eavm512/ME396P-F2022-G03/Standards/brainstorm data structure/board-class-rack.jpeg

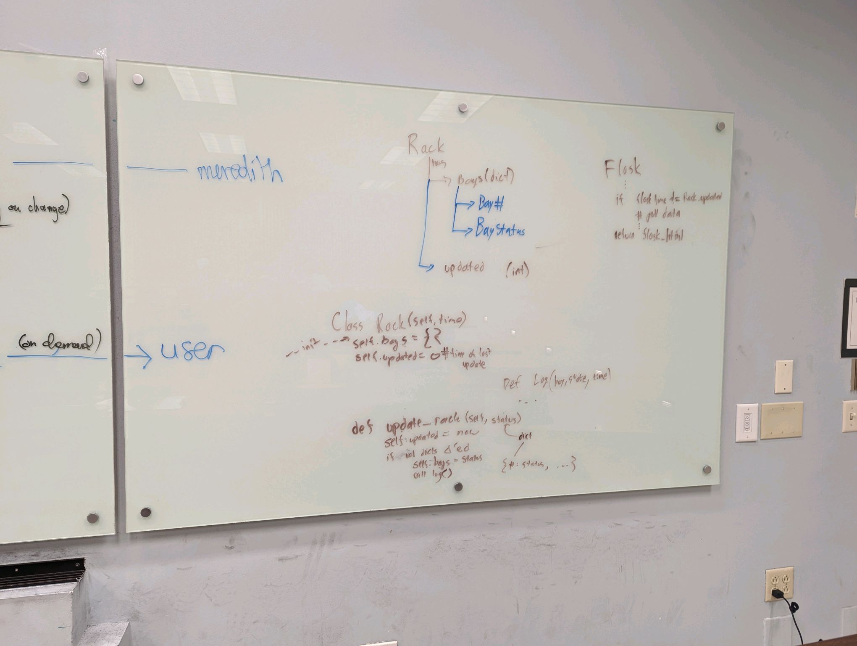
Standards/brainstorm data structure/board-class-rack.jpeg
