eavm512/ME396P-F2022-G03/Lightning Talk and Demo-test files/basic_arduino_game/basic_arduino_game.png

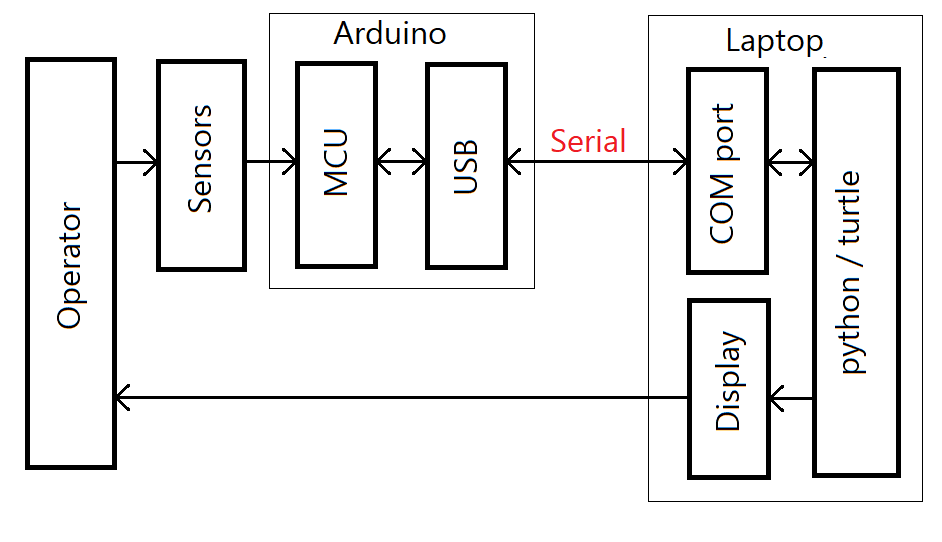
Lightning Talk and Demo-test files/basic_arduino_game/basic_arduino_game.png
