eavm512/ME396P-F2022-G03/Lightning Talk and Demo-test files/button-LED.png

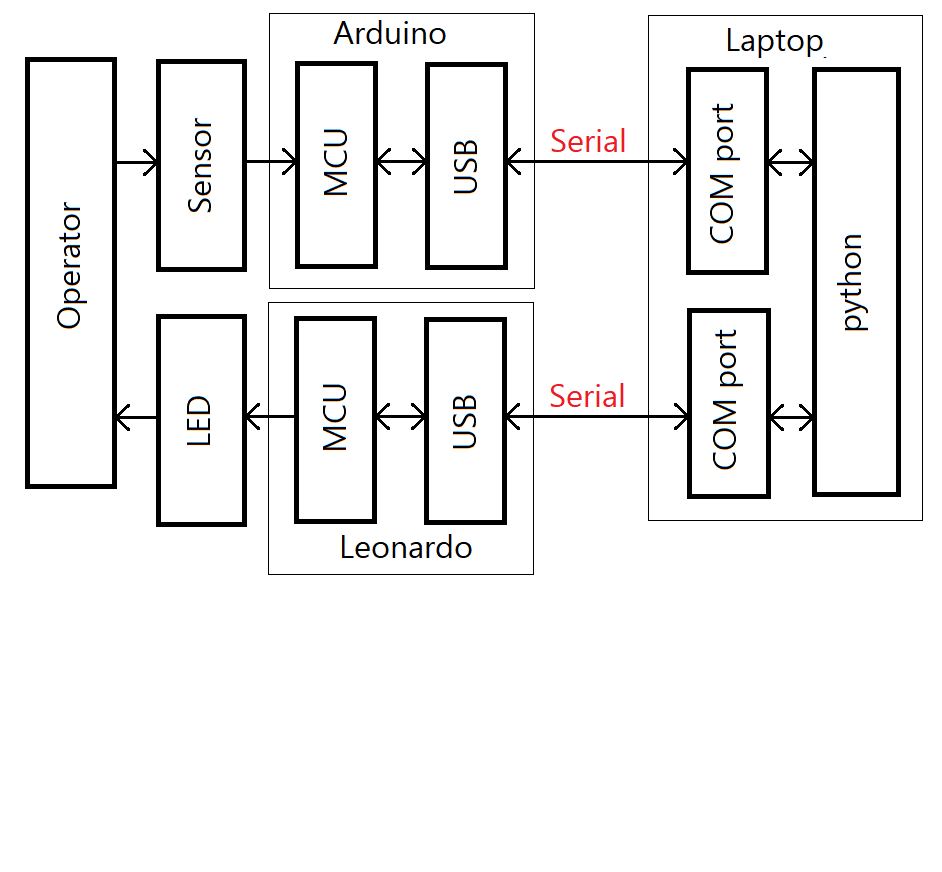
Lightning Talk and Demo-test files/button-LED.png
