eavm512/ME396P-F2022-G03/Lightning Talk and Demo-test files/basic_arduino_game/basic_game_controller.py

# -*- coding: utf-8 -*-
"""
Python 3.7
Created on Sat Oct  8 10:24:00 2022

@author: casso
"""

import serial
import turtle
import time

# ser = serial.Serial('COM3', 9600)

# ser
# Out[5]: Serial<id=0x254b51f4c70, open=True>(port='COM3', baudrate=9600, bytesize=8, parity='N', stopbits=1, timeout=None, xonxoff=False, rtscts=False, dsrdtr=False)

# ser.readline()
# Out[6]: b'17697\r\n'

#go get some test input lines
# ser = serial.Serial('COM3', 9600)
# lines = []
# while len(lines) < 10:
#     lines.append(ser.readline())
    
# #parse the lines
# messages = []
# for line in lines:
#     message = ''
#     decoded = bytes.decode(line)
    
#     for char in decoded:
#         if char != '\n' and char != '\r':
#             message = message + char
    
#     messages.append(message)
    
# #see how we did
# print(messages)
#   ['108', 'FIRE!', '153', '133', '147', '233', 'FIRE!', '273', '290', 'FIRE!']
# ser.close()

def test_serial(ser):
    lines = []
    while len(lines) < 10:
        lines.append(ser.readline())
        
    #parse the lines
    messages = []
    for line in lines:
        message = ''
        decoded = bytes.decode(line)
        
        for char in decoded:
            if char != '\n' and char != '\r':
                message = message + char
        
        messages.append(message)
    
    return messages

def parse_msg(msg_str):
    msg_str = bytes.decode(msg_str)
    msg = ''
    for char in msg_str:
        if char != '\n' and char != '\r':
            msg += char
    return msg

def shoot(current_angle):
    '''shoot a projectile
    '''
    missile = turtle.Turtle()
    missile.lt(current_angle)
    missile.penup()
    
    #make it a laser if we're in laser mode
    if projectile_mode == 'laser':
        missile.speed(speed = 0) #spin laser turtle FAST
        missile.pendown()
        missile.pen(fillcolor = 'red', pencolor = 'red')
        missile.ht() #hide the turtle     
    
    return missile

def draw(msg, missiles, last_heading, projectile_mode):
    '''
    rotate the player
    advance any missiles
    remove any missiles that have gone too far
    '''
    print(msg)    

    
    if msg != 'FIRE!' and msg != 'Toggle mode':
        last_heading = int(msg)
        player.settiltangle(last_heading)
    elif 'Toggle mode' in msg:
        if projectile_mode == 'arrow': 
            projectile_mode = 'laser'
        else: 
            projectile_mode = 'arrow'
    else: #we're firing a missile!
        new_missile = shoot(last_heading)
        missiles.append(new_missile)
        print('pew!')
    
    #advance existing missiles
    for miss in missiles:
        if miss.pencolor() == 'red':
            miss.forward(LASER_SPEED)
        else:
            miss.forward(MISSILE_SPEED)

    
    #remove missiles that are far away:
    #someone help me with a better way to do this!
    to_remove = []
    for idx in range(0, len(missiles)):
        if missiles[idx].distance(0,0) > MISSILE_DELETE:
            to_remove.append(idx)
            
    to_remove.reverse()
    for remove_idx in to_remove:
        missiles[remove_idx].reset()
        missiles[remove_idx].ht() #hide the turtle
        del missiles[remove_idx]
    
    
    return missiles, last_heading, projectile_mode

#--------------------------------------------------
MISSILE_DELETE = 220
MISSILE_SPEED  = 10
MISSILE_COLOR  = 'off'
LASER_SPEED = 200
LASER_TRAIL = 'red'
TURTLE_SPEED = 1 #Faster than turtle's default. pick 0-10, 0 fastest

projectile_mode = 'arrow'
projectile_speed = MISSILE_SPEED
projectile_color = 'off'

ser =serial.Serial('COM3', 9600)

player = turtle.Turtle()
player.shape('turtle')
player.color('green')
player.speed(speed = TURTLE_SPEED)
missiles = [] #a list of turtle missiles
window = turtle.Screen()
last_heading = 0

while(True):
    missiles, last_heading, projectile_mode = draw(parse_msg(ser.readline()), 
                                  missiles, last_heading, projectile_mode)
    time.sleep(.05)
    
    if len(missiles) > 5:
        print("so many missiles! goodbye")
        break


turtle.bye()
ser.close()
