eavm512/ME396P-F2022-G03/Lightning Talk and Demo-test files/blink/blink/serial_interface.h

 { 'R', "blink_high", "K?", "tell python that we are ready to play" },
 { 'H', "blink_high", "K?", "tell python that the LED was set high" },
 { 'L', "blink_low", "K?", "tell python that the LED was set low" },
